cesau78/tektonology/3d-models/prayer-sole/v3-compound-fastened/sole-prayers/jerome-lucido/jerome-lucido-tread-body.stl

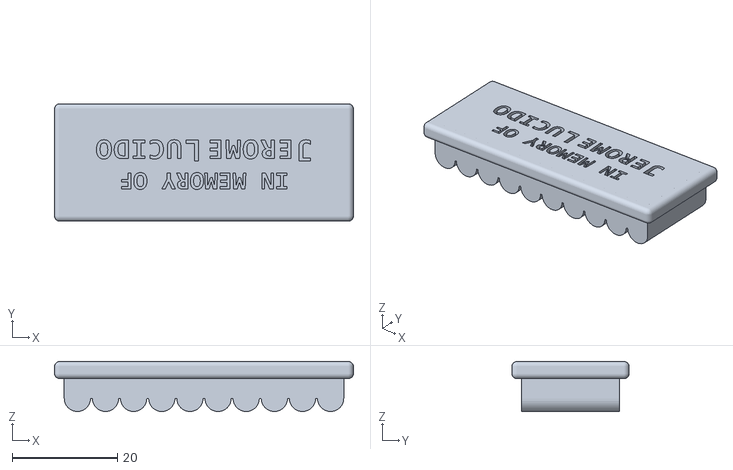
[picture p15: CAD file, 2026-05-01]
3d-models/prayer-sole/v3-compound-fastened/sole-prayers/jerome-lucido/jerome-lucido-tread-body.stl
56.8 x 22.3 x 9.50
