cesau78/tektonology/3d-models/prayer-sole/v3-compound-fastened/sole-prayers/praise-the-lord/praise-the-lord-tread-body.stl

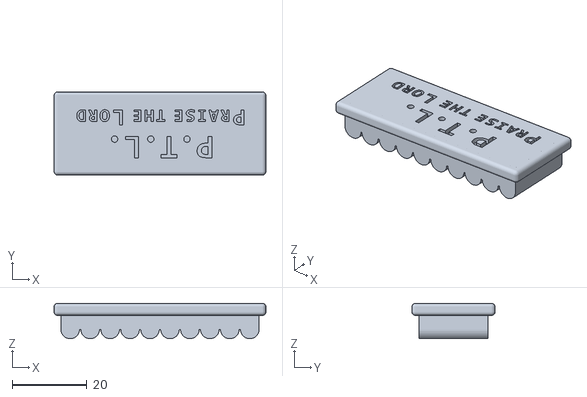
[picture p16: CAD file, 2026-04-18]
3d-models/prayer-sole/v3-compound-fastened/sole-prayers/praise-the-lord/praise-the-lord-tread-body.stl
56.8 x 22.3 x 9.50
