cesau78/tektonology/3d-models/ptfe-port-dryer-box/ptfe-port-dryer-box.stl

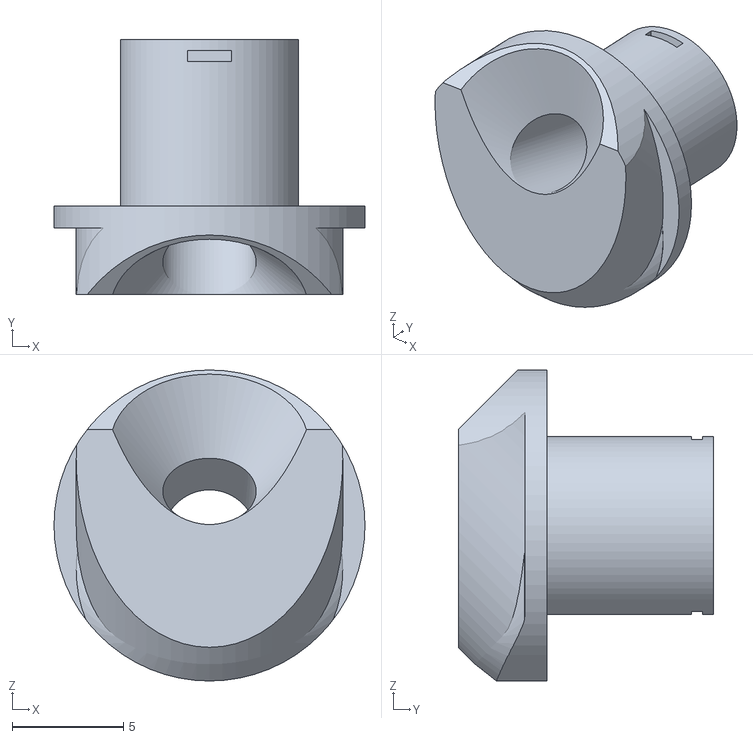
[picture p17: CAD file, 2026-03-22]
3d-models/ptfe-port-dryer-box/ptfe-port-dryer-box.stl
14.0 x 11.5 x 14.0
