cesau78/tektonology/3d-models/ptfe-port-printer-tent/ptfe-port-printer-tent-collar.stl

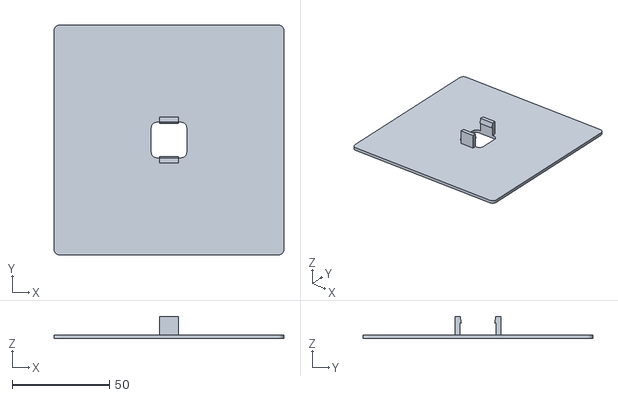
[picture p18: CAD file, 2026-04-04]
3d-models/ptfe-port-printer-tent/ptfe-port-printer-tent-collar.stl
118.0 x 118.0 x 11.5
