cesau78/tektonology/liquid-bait-station/liquid-bait-station.stl

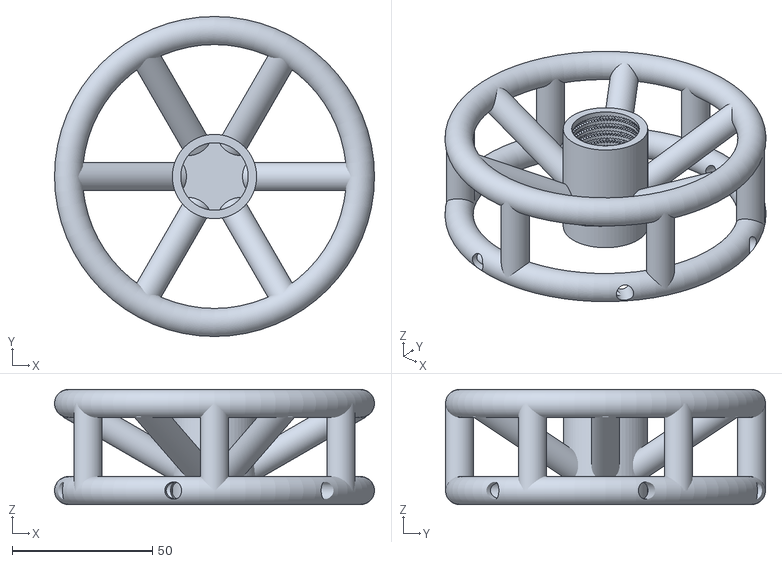
[picture p19: CAD file, 2026-02-21]
liquid-bait-station/liquid-bait-station.stl
113.9 x 113.9 x 41.0
