cesau78/tektonology/tektonology-spa/public/stl/collar.stl

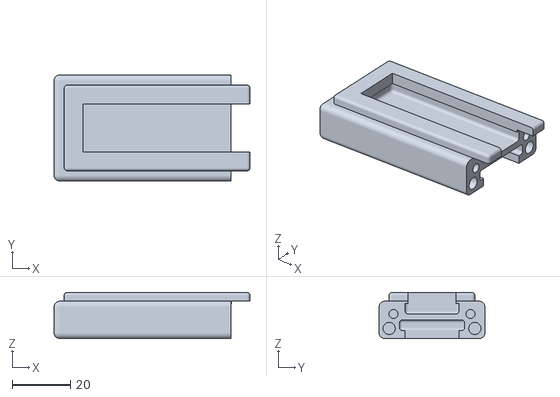
[picture p20: CAD file, 2026-06-22]
tektonology-spa/public/stl/collar.stl
67.5 x 36.5 x 15.8
