cesau78/tektonology/3d-models/notecard-holder/notecard-holder-divider.stl

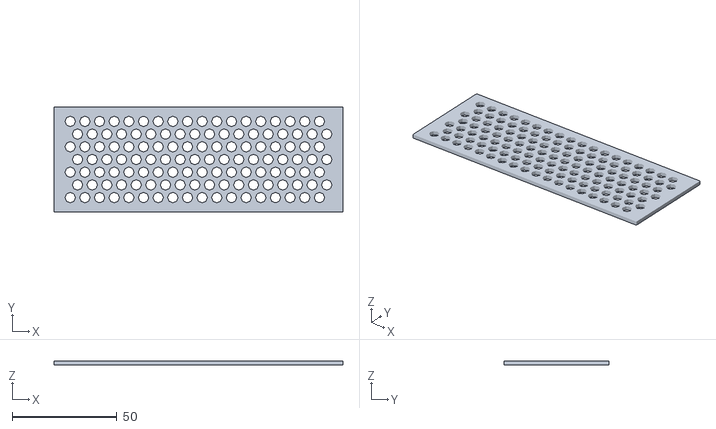
[picture p21: CAD file, 2026-03-11]
3d-models/notecard-holder/notecard-holder-divider.stl
138.0 x 50.3 x 2.00
