cesau78/tektonology/3d-models/prayer-sole/v2-compound-bonded/kneeler-boot-coupler.stl

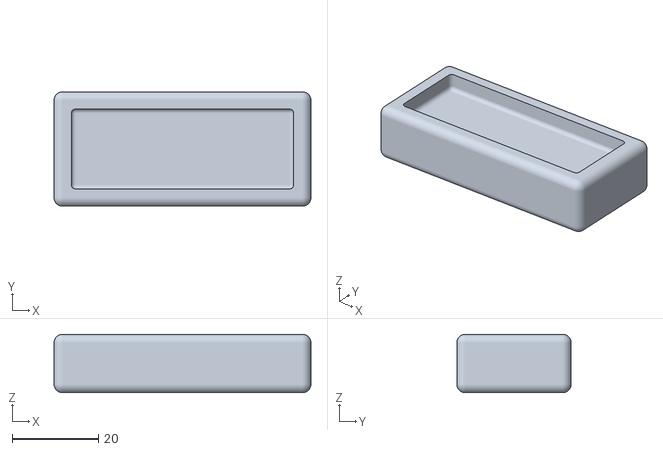
[picture p22: CAD file, 2026-02-20]
3d-models/prayer-sole/v2-compound-bonded/kneeler-boot-coupler.stl
59.5 x 26.5 x 13.5
