cesau78/tektonology/3d-models/prayer-sole/v3-compound-fastened/latest-builds/v3.9.6/collar.stl

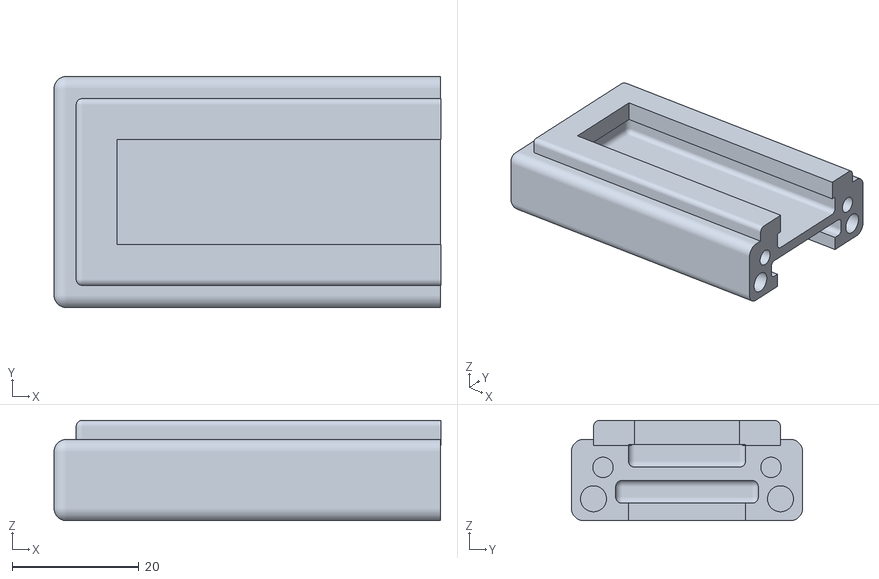
[picture p23: CAD file, 2026-07-21]
3d-models/prayer-sole/v3-compound-fastened/latest-builds/v3.9.6/collar.stl
61.0 x 36.5 x 15.8
