cesau78/tektonology/3d-models/prayer-sole/v3-compound-fastened/sole-prayers/pospie-memorial/pospie-memorial-tread-text.stl

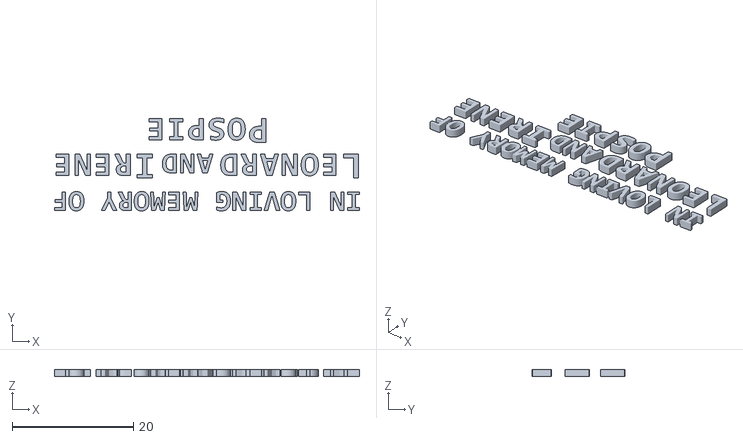
[picture p24: CAD file, 2026-04-18]
3d-models/prayer-sole/v3-compound-fastened/sole-prayers/pospie-memorial/pospie-memorial-tread-text.stl
50.3 x 15.3 x 1.21
