cesau78/tektonology/3d-models/prayer-sole/v3-compound-fastened/sole-prayers/praise-the-lord/praise-the-lord-tread-text.stl

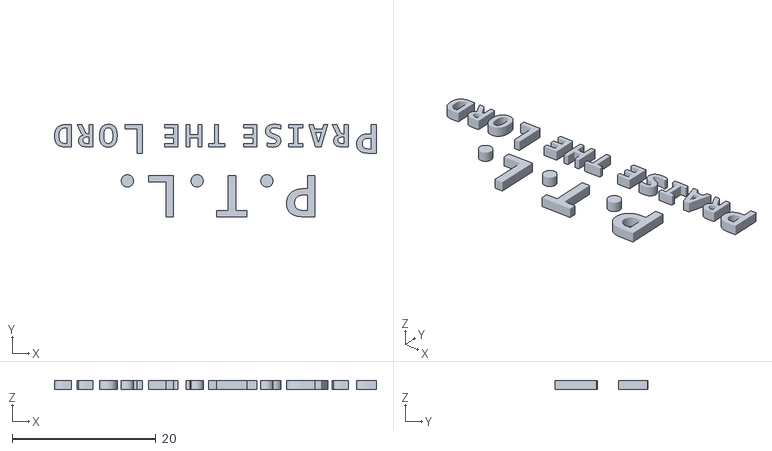
[picture p25: CAD file, 2026-04-18]
3d-models/prayer-sole/v3-compound-fastened/sole-prayers/praise-the-lord/praise-the-lord-tread-text.stl
44.8 x 12.9 x 1.21
