cesau78/tektonology/3d-models/prayer-sole/v3-compound-fastened/sole-prayers/tektonology/tektonology-tread-text.stl

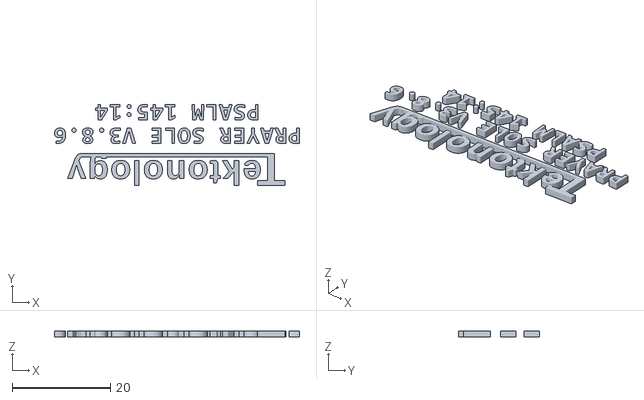
[picture p26: CAD file, 2026-04-18]
3d-models/prayer-sole/v3-compound-fastened/sole-prayers/tektonology/tektonology-tread-text.stl
49.8 x 16.5 x 1.21
