cesau78/tektonology/3d-models/ptfe-port-printer-tent/ptfe-port-printer-tent-shaft.stl

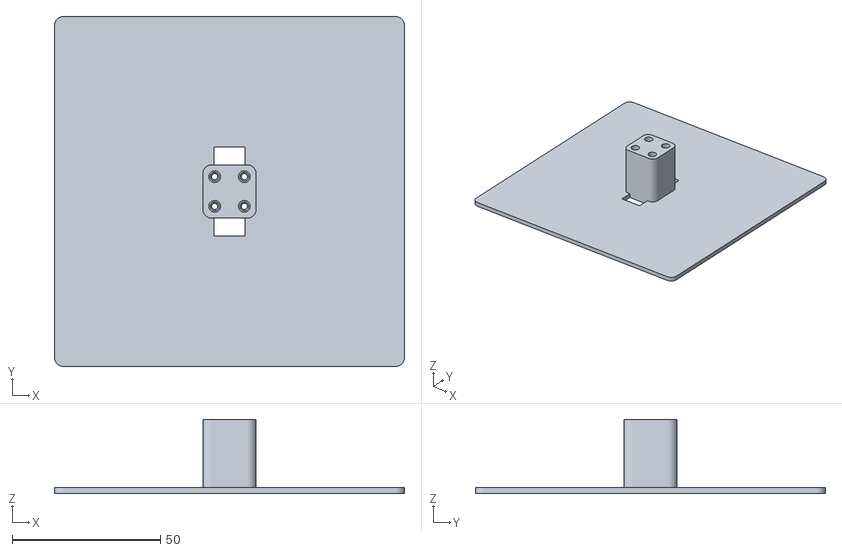
[picture p27: CAD file, 2026-04-04]
3d-models/ptfe-port-printer-tent/ptfe-port-printer-tent-shaft.stl
118.0 x 118.0 x 25.0
