cesau78/tektonology/tektonology-spa/public/stl/cap.stl

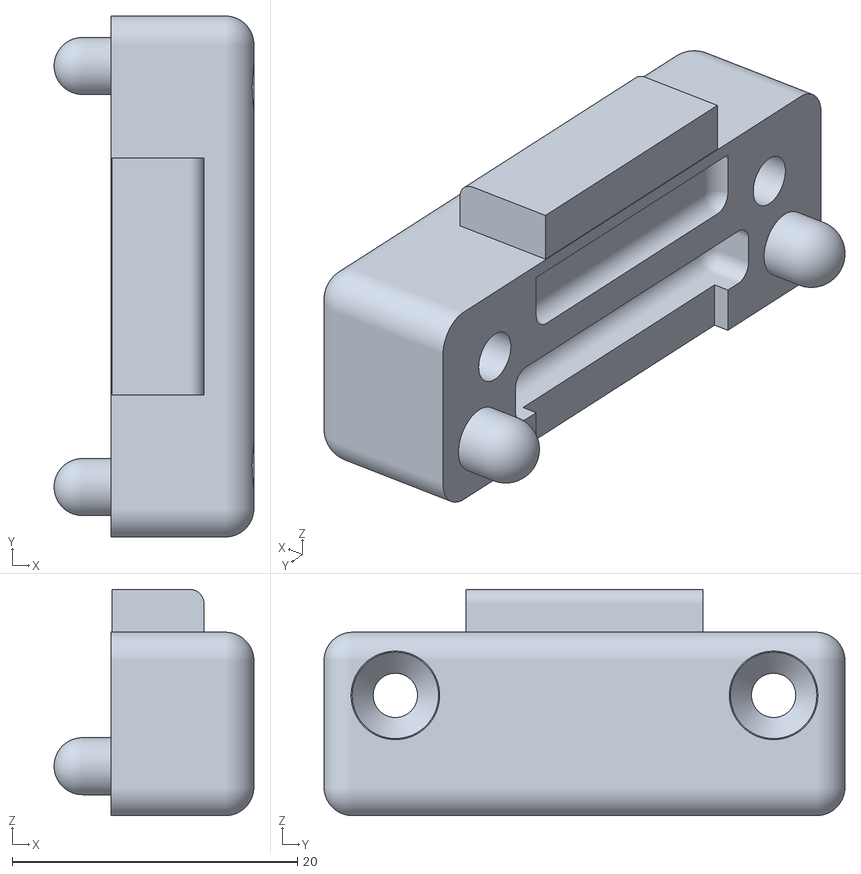
[picture p28: CAD file, 2026-06-22]
tektonology-spa/public/stl/cap.stl
14.0 x 36.5 x 15.8
