cesau78/tektonology/3d-models/notecard-holder/notecard-holder-side.stl

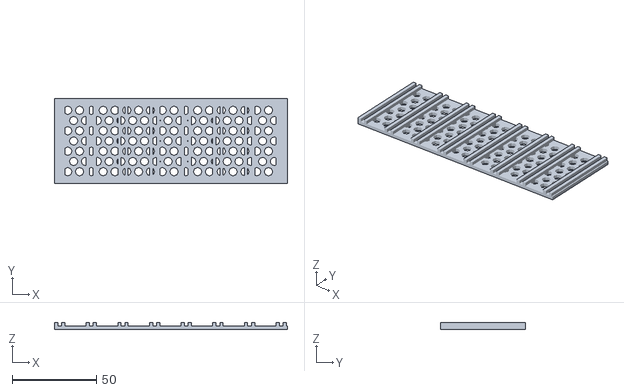
[picture p29: CAD file, 2026-03-11]
3d-models/notecard-holder/notecard-holder-side.stl
138.1 x 50.3 x 4.00
