cesau78/tektonology/tektonology-spa/public/stl/kneeler-bracket-left.stl

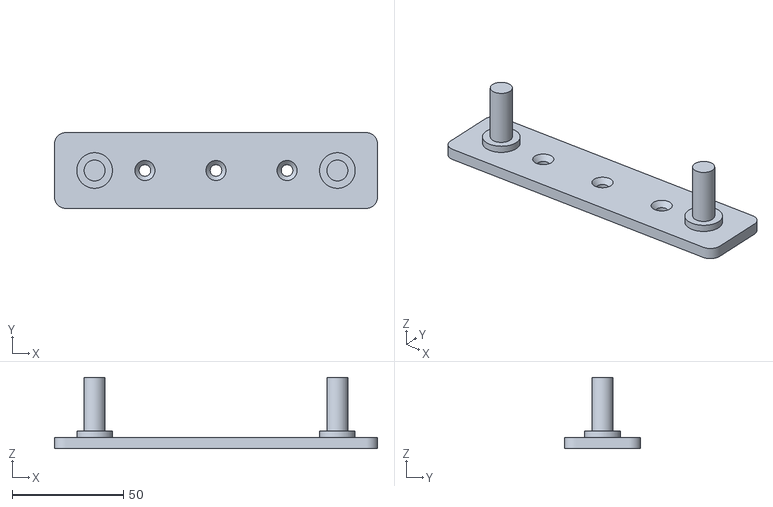
[picture p30: CAD file, 2026-05-03]
tektonology-spa/public/stl/kneeler-bracket-left.stl
145.0 x 34.0 x 32.0
