cesau78/tektonology/tektonology-spa/public/stl/kneeler-boot-slipper.stl

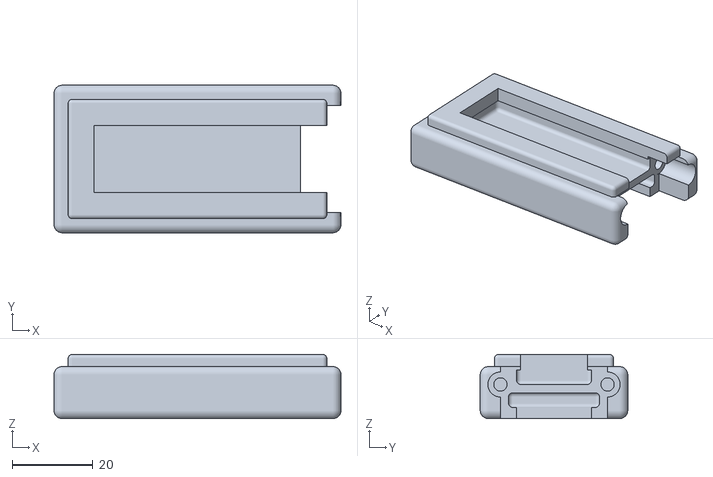
[picture p31: CAD file, 2026-03-23]
tektonology-spa/public/stl/kneeler-boot-slipper.stl
71.0 x 36.5 x 15.8
