cesau78/tektonology/tektonology-spa/public/stl/allen-wrench-handle.stl

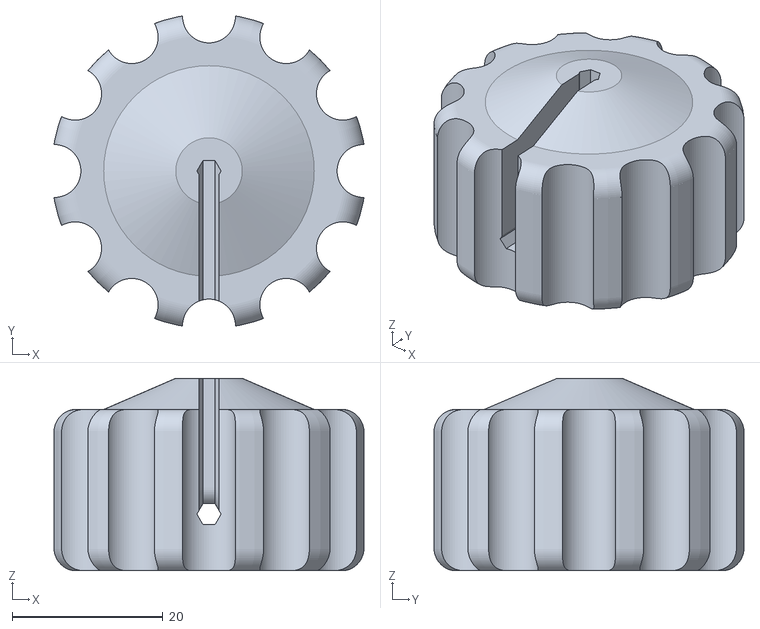
[picture p32: CAD file, 2026-03-20]
tektonology-spa/public/stl/allen-wrench-handle.stl
41.1 x 41.1 x 25.5
