cesau78/tektonology/tektonology-spa/public/stl/kneeler-boot-cap.stl

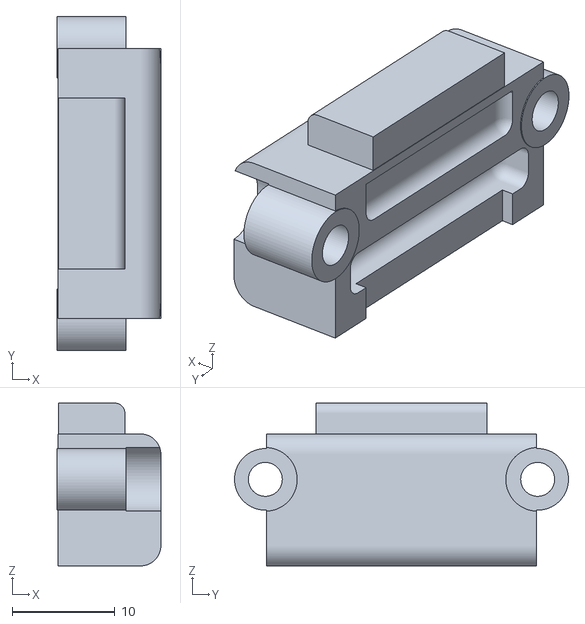
[picture p33: CAD file, 2026-03-14]
tektonology-spa/public/stl/kneeler-boot-cap.stl
10.1 x 32.5 x 15.8
