cesau78/tektonology/3d-models/kneeler-replacement-parts/kneeler-boot-compound-fastened/kneeler-boot-config.scad

// --- TEKTONOLOGY KNEELER BOOT CONFIG ---
// Shared parameters and modules for the 2-piece coupler (slipper + cap)

tolerance = 0.1; // general tolerance for fit adjustments (mm)

// --- Sole Plate Dimensions ---
sole_plate_l = 53;
sole_plate_w = 18.5;
sole_plate_h = 3.5;

// --- Leg Dimensions (for socket fit) ---
leg_w = 16.5;
leg_l = 51;

// --- Bottom Slide Groove (shared between coupler + insert) ---
groove_overhang = 2;      // groove extends this far beyond socket per side

// --- Performance Settings ---
preview = false; //set preview=true for faster rendering with lower detail, or false for full detail.
crosssection_view = false; // Set to true to cut the model along a plane and show only one side
crosssection_axis = "y"; // axis: 'x', 'y', or 'z'
crosssection_pos = 12; // position (mm) along the chosen axis where the cut occurs (default 0 = origin)

// --- Shell Geometry ---
wall = 9.0; // thicker walls to house M3 hardware in the side walls
floor_thickness = 3.0; // thickness of the shell floor under the bottom socket

bottom_target_depth = 6.35;
total_h = sole_plate_h + bottom_target_depth + floor_thickness;
r = 2.0;
$fn = preview ? 32 : 64;

// --- Lip Parameters ---
enable_top_lip = true;
lip_inset = 1;
lip_thickness = 3;
lip_height = 1;  // Z thickness of cap lip relief cut in slipper

// --- Two-Piece Split ---
cap_thickness = 8; // along X axis
split_x = (sole_plate_l / 2) + wall - r - cap_thickness;

// --- Derived ---
outer_extent = (sole_plate_l / 2) + wall; // half-length of outer shell after minkowski
cap_width = sole_plate_w + (groove_overhang * 2) + 4; // cap Y width matches bottom groove (including minkowski)
// Lip ring inner opening dimensions (used for lip splitting)
lip_inner_x = leg_l + tolerance;
lip_inner_y = leg_w + tolerance; // add some clearance around the leg for easy fit and print tolerance

// --- M3x30 Socket Head Cap Screw Hardware ---
bolt_dia        = 3.0;
bolt_clearance  = 0.3;  // clearance for bolt holes (0 for snug fit, increase if needed for print tolerance)
bolt_length     = 20;   // M3x20 — shaft length under head (very common size)
nut_af          = 5.5;  // hex nut across-flats
nut_clearance   = 0.2;  // clearance for nut pockets
nut_thickness   = 2.4;  // typical M3 nut thickness, adjust if using thinner/heavier nuts
head_dia        = 6.0;  // M3 socket head cap screw head diameter
head_clearance  = tolerance;
head_height     = 3.5;   // M3 socket head height

// Nut X position: derived so bolt tip fully engages the nut with 0.5mm margin
// bolt shaft starts at outer_extent - head_height, tip = start - bolt_length
nut_x = (outer_extent - head_height) - bolt_length + (nut_thickness / 2) + 0.5;

// Bolt position: two screws aligned with cap side bosses (Y = ±cap_width/2)
bolt_z = (bolt_dia / 2) + 0.5; // bottom of bolt hole 0.5mm above z=0
bolt_positions = [[bolt_z, cap_width / 2], [bolt_z, -cap_width / 2]];

// --- Cap Side Bosses ---
boss_dia       = head_dia;    // matches cap screw head diameter
boss_height    = head_height; // adjust with screw availability
boss_clearance = tolerance; // clearance per side between cap boss and slipper socket

// --- Alignment Tongue ---
tongue_width     = 10;   // along Y
tongue_height    = 6;    // along Z
tongue_depth     = 1.5;  // protrusion along X
tongue_clearance = tolerance;

// --- Big constant for half-space clipping ---
big = 200;

// =====================================================================
// COUPLER SHELL — outer shell + sockets, WITHOUT the top lip
// =====================================================================
module coupler_shell() {
    module inner_cuts() {
        // TOP SOCKET (Metal Leg) — beveled/rounded walls
        translate([0, 0, (total_h / 2) - (sole_plate_h / 2) + tolerance])
            minkowski() {
                cube([leg_l, leg_w, sole_plate_h], center=true);
                sphere(r=1.0);
            }

        // BOTTOM SOCKET (TPU Plug) — flat walls
        translate([0, 0, -(total_h / 2) + (bottom_target_depth / 2) - tolerance])
            cube([sole_plate_l, sole_plate_w, bottom_target_depth + 0.2], center=true);

        // BOTTOM SOCKET SLIDE GROOVE — rounded perimeter, wider than socket for slide-in rail
        // 1/4 socket depth, top aligned to top of bottom socket
        groove_h = bottom_target_depth / 4;
        translate([0, 0, -(total_h / 2) + bottom_target_depth - (groove_h / 2) - 1])
            minkowski() {
                cube([
                    sole_plate_l + (groove_overhang * 2) - 2,
                    sole_plate_w + (groove_overhang * 2) - 2,
                    groove_h
                ], center=true);
                sphere(r=1.0);
            }
    }

    difference() {
        minkowski() {
            cube([
                sole_plate_l + (wall * 2) - (r * 2),
                sole_plate_w + (wall * 2) - (r * 2),
                total_h - (r * 2)
            ], center=true);
            sphere(r=r);
        }
        inner_cuts();
    }
}

// =====================================================================
// TOP SOCKET CUT — reusable for re-cutting after lip is added
// =====================================================================
module top_socket_cut() {
    // Flat cut — shaves 2*tolerance off the underside of the lip
    cut_h = tolerance * 2;
    lip_r = 1.0;
    lip_bottom_z = (total_h / 2) - lip_r + (lip_thickness / 2) - (lip_thickness / 2);
    translate([0, 0, lip_bottom_z + (cut_h / 2)])
        cube([sole_plate_l, sole_plate_w, cut_h], center=true);
}

// =====================================================================
// TOP LIP — standalone module (full rectangular ring)
// =====================================================================
module top_lip() {
    lip_r = 1.0; // Minkowski rounding radius for lip
    // Positioned so flat bottom overlaps shell top by lip_r for bonded fit
    lip_z = (total_h / 2) - lip_r + (lip_thickness / 2);
    cut_z = lip_z - (lip_thickness / 2); // flat bottom plane
    outer_x = sole_plate_l + wall;
    outer_y = sole_plate_w + wall;

    intersection() {
        translate([0, 0, lip_z])
        difference() {
            minkowski() {
                cube([outer_x, outer_y, lip_thickness], center=true);
                sphere(r=lip_r);
            }
            // Ring cutout
            cube([lip_inner_x, lip_inner_y, lip_thickness + 2], center=true);
            // Underside relief
            translate([0, 0, -(lip_thickness / 2) - 1])
                minkowski() {
                    cube([leg_l, leg_w, 0.01], center=true);
                    sphere(r=lip_r);
                }
        }
        // Remove bottom Minkowski rounding for flat bonded fit to slipper
        translate([-big, -big, cut_z])
            cube([big * 2, big * 2, big * 2]);
    }
}

// =====================================================================
// SPLIT LIP MODULES
// =====================================================================

// Slipper lip: full ring MINUS the far short-end bar (cap's portion).
module slipper_lip() {
    intersection() {
        top_lip();
        union() {
            translate([-big, -big, -big])
                cube([big + lip_inner_x / 2, big * 2, big * 2]);
            translate([-big, lip_inner_y / 2, -big])
                cube([big * 2, big, big * 2]);
            translate([-big, -big - lip_inner_y / 2, -big])
                cube([big * 2, big, big * 2]);
        }
    }
}

// Cap lip: only the far short-end bar between the slipper's overhanging lips.
module cap_lip() {
    intersection() {
        top_lip();
        translate([lip_inner_x / 2, -lip_inner_y / 2, -big])
            cube([big, lip_inner_y, big * 2]);
    }
}

// =====================================================================
// HALF-SPACE helpers
// =====================================================================

module slipper_half_space() {
    translate([-big, -big, -big])
        cube([big + split_x, big * 2, big * 2]);
}

module cap_half_space() {
    translate([split_x, -big, -big])
        cube([big, big * 2, big * 2]);
}

// Side-wall Y bands (material outside the cap width)
module side_bands() {
    // +Y band
    translate([-big, cap_width / 2, -big])
        cube([big * 2, big, big * 2]);
    // -Y band
    translate([-big, -big - cap_width / 2, -big])
        cube([big * 2, big, big * 2]);
}

// Center Y band (material inside the socket footprint)
module center_band() {
    translate([-big, -sole_plate_w / 2, -big])
        cube([big * 2, sole_plate_w, big * 2]);
}

// =====================================================================
// CROSS-SECTION SUPPORT
// =====================================================================
module crosssection(half_space) {
    if (!crosssection_view) {
        children();
    } else {
        intersection() {
            children();
            if (crosssection_axis == "x")
                translate([crosssection_pos, -half_space, -half_space])
                    cube([half_space * 2, half_space * 2, half_space * 2]);
            if (crosssection_axis == "y")
                translate([-half_space, crosssection_pos, -half_space])
                    cube([half_space * 2, half_space * 2, half_space * 2]);
            if (crosssection_axis == "z")
                translate([-half_space, -half_space, crosssection_pos])
                    cube([half_space * 2, half_space * 2, half_space * 2]);
        }
    }
}

// =====================================================================
// DEBUG: visualize hex nuts in their pockets
// =====================================================================
module debug_nuts() {
    nut_r = nut_af / 2 / cos(30);
    color("green", 0.7)
        for (pos = bolt_positions) {
            rot = (pos[1] > 0) ? 15 : -15; // mirror matches slipper's mirror([0,m,0])
            translate([nut_x, pos[1], pos[0]])
                rotate([0, 90, 0])
                    rotate([0, 0, rot])
                        cylinder(h=nut_thickness, r=nut_r, $fn=6, center=true);
        }
}

// =====================================================================
// DEBUG: visualize bolts in their holes
// =====================================================================
module debug_bolts() {
    head_start_x = outer_extent - head_height;
    color("yellow", 0.7)
        for (pos = bolt_positions) {
            // Shaft
            translate([head_start_x - bolt_length, pos[1], pos[0]])
                rotate([0, 90, 0])
                    cylinder(h=bolt_length, d=bolt_dia, center=false);
            // Socket head
            translate([head_start_x, pos[1], pos[0]])
                rotate([0, 90, 0])
                    cylinder(h=head_height, d=head_dia, center=false);
        }
}
