cesau78/tektonology/3d-models/bumper-bracket/bumper-bracket.scad

// Bumper bracket body: shell envelope (core + roof wedge + pew pad) pre-mink, then fillet + cutters.
// Drawn in bracket coordinates (see config.scad). No rotate() reorients the bracket body.

include <config.scad>

// Includers (cap.scad, tread-carriage.scad, …) set BUMPER_BRACKET_INCLUDED_BY = true
// before `include <bumper-bracket.scad>` so only the host file emits root geometry.
$fn = preview ? 32 : 64;

// Core, roof overlap + prism, and pew pad — shared envelope anchors, no per-part minkowski.
module shell_envelope_pre_mink(overlap_below = corner_r) {
    core_c = shell_envelope_core_center_lxlz();
    wedge_xr = shell_envelope_wedge_xr_lx_mm();
    wedge_run = shell_inset_dim_qr_wedge_mm;
    wedge_depth = shell_inset_dim_tread_pew_mm;

    intersection() {
        union() {
            translate(bracket_pos(core_c[0], core_c[1], core_c[2]))
                cube(
                    [shell_envelope_core_lx_mm, shell_envelope_core_lz_mm, shell_envelope_core_ly_mm],
                    center = true
                );

            translate(bracket_pos(
                shell_envelope_inset_lx_mm + wedge_run / 2,
                shell_envelope_inset_ly_mm + wedge_depth / 2,
                shell_envelope_roof_lz_mm - overlap_below / 2
            ))
                cube([wedge_run, overlap_below, wedge_depth], center = true);

            polyhedron(
                points = [
                    bracket_pos(shell_envelope_inset_lx_mm, shell_envelope_inset_ly_mm, shell_envelope_roof_lz_mm),
                    bracket_pos(wedge_xr, shell_envelope_inset_ly_mm, shell_envelope_roof_lz_mm),
                    bracket_pos(wedge_xr, shell_envelope_inset_ly_mm, shell_envelope_apex_lz_mm),
                    bracket_pos(shell_envelope_inset_lx_mm, shell_envelope_inset_ly_mm + wedge_depth, shell_envelope_roof_lz_mm),
                    bracket_pos(wedge_xr, shell_envelope_inset_ly_mm + wedge_depth, shell_envelope_roof_lz_mm),
                    bracket_pos(wedge_xr, shell_envelope_inset_ly_mm + wedge_depth, shell_envelope_apex_lz_mm),
                ],
                faces = [
                    [0, 1, 4, 3],
                    [1, 2, 5, 4],
                    [0, 3, 5, 2],
                    [0, 2, 1],
                    [3, 4, 5],
                ],
                convexity = 4
            );

            // Front (+Y) end extended by pew_mount_block_face_extend_y_mm and tilted by
            // pew_mount_block_face_angle_deg, built straight into the pre-mink primitive as
            // an extruded X-Y footprint (front edge follows the tilt line). This way the
            // angle gets the same minkowski rounding and renders cleanly — no post-mink cut.
            if (pew_mount_block_enabled && pew_mount_block_y_len_mm > 0.2) {
                blk_x_lo = pew_mount_block_x_center_mm() - pew_mount_block_thickness_x_mm / 2;
                blk_x_hi = pew_mount_block_x_center_mm() + pew_mount_block_thickness_x_mm / 2;
                blk_y_lo = pew_mount_block_y_lo_mm();
                translate([0, 0, pew_mount_block_z_center_mm() - pew_mount_block_z_len_mm() / 2])
                    linear_extrude(pew_mount_block_z_len_mm())
                        polygon([
                            [blk_x_lo, blk_y_lo],
                            [blk_x_hi, blk_y_lo],
                            [blk_x_hi, pew_mount_block_front_y_at(blk_x_hi)],
                            [blk_x_lo, pew_mount_block_front_y_at(blk_x_lo)],
                        ]);
            }

            // Reinforcement welded to the block's −X side: full block Z height, from the
            // roof-wedge start out to the block's tilted +Y front. A pre-mink primitive so
            // it rounds and welds flush; its front edge shares the same tilt line as the block.
            if (pew_mount_reinforce_enabled && pew_mount_block_enabled && pew_mount_block_y_len_mm > 0.2) {
                rx_hi = pew_mount_block_x_center_mm() - pew_mount_block_thickness_x_mm / 2;
                rx_lo = rx_hi - pew_mount_reinforce_depth_x_mm;
                ry_lo = bracket_nat_y_mid_mm - shell_height_mm;   // roof-wedge start (core/wedge seam)
                translate([0, 0, pew_mount_block_z_center_mm() - pew_mount_block_z_len_mm() / 2])
                    linear_extrude(pew_mount_block_z_len_mm())
                        polygon([
                            [rx_lo, ry_lo],
                            [rx_hi, ry_lo],
                            [rx_hi, pew_mount_block_front_y_at(rx_hi)],
                            [rx_lo, pew_mount_block_front_y_at(rx_lo)],
                        ]);
            }

        }

        // Rectangular hull clip: remove all geometry below y = -25 before minkowski.
        // Hull of two large flat slabs produces a clean rectangular prism y ≥ -25.
        _pre_mink_y_floor_hull();
    }
}

module _pre_mink_y_floor_hull() {
    big = _bracket_cross_half_extent();
    hull() {
        translate([-big, -25, -big]) cube([2 * big, 1, 2 * big]);
        translate([-big,  big, -big]) cube([2 * big, 1, 2 * big]);
    }
}

// Two hull cutters, one per gap between the 3 roof screws (fracs 1/6, 1/2, 5/6).
// Centered at inter-screw midpoints (fracs 1/3 and 2/3), Z height = half the
// inter-screw spacing. Subtracted pre-minkowski so cut edges get the sphere fillet.
module _pre_mink_screw_gap_tabs_cut() {
    tab_z_half = shell_inset_dim_tread_pew_mm / 12;
    for (pair = [
        [-screw_gap_tab_z_nudge_mm, 1/3],   // bottom tab, shifted −Z
        [ screw_gap_tab_z_nudge_mm, 2/3],   // top tab, shifted +Z
    ])
        _pre_mink_screw_gap_tab(
            corner_r + shell_inset_dim_tread_pew_mm * pair[1] - shell_extent_tread_pew_mm / 2 + pair[0],
            tab_z_half
        );
}

// Rectangular hull cutter: X −20→+30, Y −25→0, Z centered at z_center ± z_half.
module _pre_mink_screw_gap_tab(z_center, z_half) {
    c = HULL_VERTEX_CUBE_MM;
    hull()
        for (x = [-20, 30], y = [-25, 0], z = [z_center - z_half, z_center + z_half])
            translate([x, y, z])
                cube(c, center = true);
}

function bracket_world_z_min() = bracket_face_tread_slot_z_mm;

// Exported carriage min Z after post-extraction −Z shave (bed lift only).
function tread_carriage_world_z_min() =
    tread_carriage_sel_z_lo_bracket() + tread_carriage_z_lo_trim_mm;

// Absolute bracket-frame selection prism for tread-carriage extraction.
module tread_carriage_selection_cube() {
    translate([
        tread_carriage_x_lo_mm,
        tread_carriage_y_lo_mm,
        tread_carriage_sel_z_lo_bracket(),
    ])
        cube([
            tread_carriage_x_hi_mm - tread_carriage_x_lo_mm,
            tread_carriage_y_hi_mm - tread_carriage_y_lo_mm,
            tread_carriage_sel_z_hi_bracket() - tread_carriage_sel_z_lo_bracket(),
        ]);
}

// Shave slabs off the extracted carriage solid; selection cube / bracket cavity unchanged.
module tread_carriage_post_extract_trim() {
    trim_margin = 10;
    difference() {
        children();
        if (tread_carriage_x_lo_trim_mm > 0)
            translate([
                tread_carriage_x_lo_mm,
                tread_carriage_y_lo_mm - trim_margin,
                tread_carriage_sel_z_lo_bracket() - trim_margin,
            ])
                cube([
                    tread_carriage_x_lo_trim_mm,
                    tread_carriage_y_hi_mm - tread_carriage_y_lo_mm + 2 * trim_margin,
                    tread_carriage_sel_z_hi_bracket() - tread_carriage_sel_z_lo_bracket()
                        + 2 * trim_margin,
                ]);
        if (tread_carriage_z_lo_trim_mm > 0)
            translate([
                tread_carriage_x_lo_mm - trim_margin,
                tread_carriage_y_lo_mm - trim_margin,
                tread_carriage_sel_z_lo_bracket(),
            ])
                cube([
                    tread_carriage_x_hi_mm - tread_carriage_x_lo_mm + 2 * trim_margin,
                    tread_carriage_y_hi_mm - tread_carriage_y_lo_mm + 2 * trim_margin,
                    tread_carriage_z_lo_trim_mm,
                ]);
    }
}

// Fused cap: union the plug into the body first, then cut screw-head recesses and
// chamfers through the combined solid. Cutting them inside earlier booleans clips
// material at exterior faces (minkowski skin, cap ∩ shell, etc.).
module shell_body_with_integrated_cap() {
    difference() {
        union() {
            children();
            tread_cap_solid(0, cut_bolt_hole = false);
        }
        shell_body_late_screw_cuts();
    }
}

// Head recesses and chamfers — subtract after the shell body (and fused cap) are united.
module shell_body_late_screw_cuts() {
    if (wood_screw_holes_enabled)
        wood_screw_chamfer_pattern();
    if (side_screw_enabled && pew_mount_block_enabled && pew_mount_block_y_len_mm > 0.2)
        side_screw_chamfer();
    if (tread_cap_enabled && !tread_cap_separate_print)
        tread_cap_bolt_hole();
}

// Full shell body minus the tread-carriage region (when split is enabled).
// Integrated cap (tread_cap_separate_print = false) always stays on the bracket.
module bumper_bracket_shell_body() {
    if (tread_carriage_split_enabled) {
        if (tread_cap_enabled && !tread_cap_separate_print)
            shell_body_with_integrated_cap()
                difference() {
                    shell_body_main_difference();
                    tread_carriage_selection_cube();
                }
        else
            difference() {
                difference() {
                    shell_body_main_difference();
                    tread_carriage_selection_cube();
                }
                shell_body_late_screw_cuts();
            }
    } else {
        shell_body_difference_wedge_bores();
    }
}

// Geometry inside tread_carriage_selection_cube() for a separate print.
module tread_carriage() {
    tread_carriage_post_extract_trim()
        intersection() {
            shell_body_main_difference();
            tread_carriage_selection_cube();
        };
}

// Export-only Z translate (not a design-frame rotation).
module tread_carriage_export_bed_lift() {
    if (bracket_lift_to_bed)
        translate([0, 0, -tread_carriage_world_z_min()])
            children();
    else
        children();
}

// Export-only Z translate (not a design-frame rotation).
module bracket_export_bed_lift() {
    if (bracket_lift_to_bed)
        translate([0, 0, -bracket_world_z_min()])
            children();
    else
        children();
}

function exploded_tread_offset_vec() = [
    exploded_tread_offset_pull[0],
    exploded_tread_offset_pull[1] + assembly_tread_vertical_auto_mm() + assembly_tread_z_trim_mm,
    exploded_tread_offset_pull[2],
];

function _bracket_cross_half_extent() =
    max(
        shell_extent_qr_wedge_mm,
        shell_extent_tread_pew_mm,
        shell_height_mm + shell_wedge_leg_mm
    ) * 2 + 40;

module _bracket_cross_half_space_positive() {
    h = _bracket_cross_half_extent();
    pos =
        (bracket_cross_axis == "x" ? 0
        : bracket_cross_axis == "y" ? shell_midplane_y_mm
        : 0) + bracket_cross_offset;
    if (bracket_cross_axis == "x")
        translate([pos, -h, -h])
            cube([2 * h, 2 * h, 2 * h]);
    else if (bracket_cross_axis == "y")
        translate([-h, pos, -h])
            cube([2 * h, 2 * h, 2 * h]);
    else
        translate([-h, -h, pos])
            cube([2 * h, 2 * h, 2 * h]);
}

module bracket_cross_trim() {
    if (!bracket_cross_section) {
        children();
    } else {
        intersection() {
            union() {
                children();
            }
            _bracket_cross_half_space_positive();
        }
    }
}

// One minkowski fillet over the pre-mink envelope union (tread ghost uses its own
// minkowski separately). Pre-mink cuts (undercut, screw-gap tabs) are subtracted
// BEFORE the sphere sweep so their edges receive the same fillet as the solid faces.
module shell_envelope_minkowski_union(undercut = false) {
    minkowski() {
        difference() {
            shell_envelope_pre_mink();
            if (undercut && pew_mount_block_undercut_enabled && pew_mount_block_enabled && pew_mount_block_y_len_mm > 0.2)
                pew_mount_block_bottom_undercut_cut();
            _pre_mink_screw_gap_tabs_cut();
        }
        sphere(r = corner_r, $fn = preview ? 16 : 24);
    }
}

// Solid rule cube minus three rectangular hull(CUBE) cutters on the 9.8° E-bevel plane (no polyhedron).
// (HULL_VERTEX_CUBE_MM lives in config.scad — the QR face-angle derivation needs it.)

function y_on_e_bevel_plane(z) =
    bracket_nat_y_mid_mm - tread_face_e_bevel_slope_k() * (bracket_face_pew_z_mm - z);

// Frustum with sloped top/bottom at y_top(z) and y_bot(z); sides vertical in Y (parallel to bevel normal stack).
module hull_rect_on_e_slope(x_lo, x_hi, z_lo, z_hi, y_top_lo, y_top_hi, y_bot_lo, y_bot_hi) {
    c = HULL_VERTEX_CUBE_MM;
    hull() {
        for (p = [
            [x_lo, y_bot_lo, z_lo],
            [x_hi, y_bot_lo, z_lo],
            [x_lo, y_bot_hi, z_hi],
            [x_hi, y_bot_hi, z_hi],
            [x_lo, y_top_lo, z_lo],
            [x_hi, y_top_lo, z_lo],
            [x_lo, y_top_hi, z_hi],
            [x_hi, y_top_hi, z_hi],
        ])
            translate(p)
                cube(c, center = true);
    }
}

// Cutter 1: E-bevel wedge above y_on_e_bevel_plane (0 at C∩E, tread_face_d_e_side_y_narrow_mm at D∩E).
module shell_tread_face_de_bevel_cut() {
    z_d = bracket_face_tread_slot_z_mm;
    z_c = bracket_face_pew_z_mm;
    y_e = bracket_nat_y_mid_mm;
    y_hi = y_e + shell_wedge_leg_mm + 40;
    x_h = shell_extent_qr_wedge_mm / 2 + shell_wedge_leg_mm + 20;

    // When the pew mount block extends in +Y past the E-bevel plane, stop the
    // bevel cutter at the block's −X face so the angled top sits flush against
    // the block's side wall instead of slicing diagonally through the cube. If
    // the −X reinforcement is present, stop at its −X face so it stays flush too.
    // The hull vertex cubes are CENTERED on the bound, so pull it in by half a
    // cube so the cut plane lands exactly ON the flush face instead of 0.25 mm
    // into it (that bite also ate into the QR front face's −X border).
    block_minus_x = pew_mount_block_x_center_mm() - pew_mount_block_thickness_x_mm / 2;
    flush_x = (pew_mount_reinforce_enabled && pew_mount_block_enabled && pew_mount_block_y_len_mm > 0.2)
        ? block_minus_x - pew_mount_reinforce_depth_x_mm
        : block_minus_x;
    x_hi = (pew_mount_block_enabled && pew_mount_block_y_len_mm > 0.2)
        ? flush_x - HULL_VERTEX_CUBE_MM / 2
        : x_h;

    hull_rect_on_e_slope(
        -x_h,
        x_hi,
        z_d,
        z_c,
        y_hi,
        y_hi,
        y_on_e_bevel_plane(z_d),
        y_on_e_bevel_plane(z_c)
    );
}

function hyp_z_at_x(x) =
    shell_wedge_leg_mm * (x - corner_r) / shell_wedge_hypotenuse_run_mm;

module wood_mount_hole_shank(y_frac) {
    psi_deg = atan2(shell_wedge_leg_mm, shell_wedge_hypotenuse_run_mm);
    $fn = preview ? 28 : 64;

    // rotate([-90,0,0]): local +Z = hypotenuse outward normal (leg, run) in bracket X–Y.
    translate(wood_screw_hole_exterior_bracket_pos(y_frac))
        rotate([0, 0, -psi_deg])
            rotate([-90, 0, 0])
                cylinder(h = wood_bored_axial_mm, d = wood_shank_clr, center = true);
}

module wood_mount_hole_chamfer(y_frac) {
    psi_deg = atan2(shell_wedge_leg_mm, shell_wedge_hypotenuse_run_mm);
    head_d = wood_head_diameter + 2 * screw_chamfer_lip_mm;
    shank_d = wood_shank_clr + epsilon * 2;
    head_r = head_d / 2;
    shank_r = shank_d / 2;
    half_ang = wood_screw_chamfer_half_angle_deg();
    flare_depth = (head_r - shank_r) / tan(half_ang);
    over = corner_r + epsilon * 4;
    $fn = preview ? 32 : 64;

    // #8 wood screw head flare: wide at exterior skin (d2), tapers −Z to shank (d1).
    // Subtracted in shell_body_late_screw_cuts() after all unions so the cone is not
    // clipped by the minkowski skin or earlier booleans.
    translate(wood_screw_hole_exterior_bracket_pos(y_frac))
        rotate([0, 0, -psi_deg])
            rotate([0, 90, 270])
                translate([0, 0, -flare_depth - over + 0.3])
                    cylinder(h = flare_depth + over, d1 = shank_d, d2 = head_d);
}

module wood_screw_shank_pattern() {
    for (yf = wood_screw_hole_y_fractions)
        wood_mount_hole_shank(yf);
}

module wood_screw_chamfer_pattern() {
    for (yf = wood_screw_hole_y_fractions)
        wood_mount_hole_chamfer(yf);
}

// Cutter 2/3: rectangular pocket; ceiling on y_on_e_bevel_plane − ceiling_drop; floor parallel below by depth_y.
module shell_tread_pocket_sloped_hull(lx_center, ly_center, pocket_w, pocket_len_ly, depth_y, ceiling_drop_mm) {
    z_d = bracket_face_tread_slot_z_mm;
    ly_lo = ly_center - pocket_len_ly / 2;
    ly_hi = ly_center + pocket_len_ly / 2;
    z_lo = min(ly_lo - shell_extent_tread_pew_mm / 2, z_d - epsilon * 4);
    z_hi = ly_hi - shell_extent_tread_pew_mm / 2;
    z_pad = epsilon * 4;

    x_lo = lx_center - shell_extent_qr_wedge_mm / 2 - pocket_w / 2;
    x_hi = x_lo + pocket_w;

    // tread_slot_face_offset_mm pushes every tread pocket −Y off the +Y base face.
    y_top_lo = y_on_e_bevel_plane(z_lo) - ceiling_drop_mm - tread_slot_face_offset_mm - epsilon;
    y_top_hi = y_on_e_bevel_plane(z_hi) - ceiling_drop_mm - tread_slot_face_offset_mm - epsilon;
    y_bot_lo = y_top_lo - depth_y - z_pad;
    y_bot_hi = y_top_hi - depth_y - z_pad;

    if (z_lo + 0.2 < z_hi && y_top_lo > y_bot_lo + 0.2 && y_top_hi > y_bot_hi + 0.2)
        hull_rect_on_e_slope(
            x_lo,
            x_hi,
            z_lo - z_pad,
            z_hi + z_pad,
            y_top_lo,
            y_top_hi,
            y_bot_lo,
            y_bot_hi
        );
}

module shell_tread_groove_pocket_cube() {
    margin_x = (shell_extent_qr_wedge_mm - groove_w) / 2;
    x_hi = shell_extent_qr_wedge_mm - margin_x;
    x_lo = x_hi - groove_w;
    y_br = tread_groove_pocket_break_tread_face_mm;
    y_len = tread_groove_pocket_inward_y_mm + y_br;
    zh = tread_groove_pocket_height_mm + epsilon * 4;
    core_zh = tread_core_pocket_depth_z_mm + epsilon * 4;
    // Cutter 2: flange groove (wider), behind tread core toward F.
    shell_tread_pocket_sloped_hull(
        tread_pocket_lx_center_mm(),
        -y_br + y_len / 2 + tread_pocket_z_nudge_mm,
        groove_w,
        y_len,
        zh,
        core_zh
    );
}

// ceiling_drop_mm = 0 → ceiling flush on E bevel (tread 1, near side). A positive
// drop sinks the pocket past the flange groove for the back-to-back tread (tread 2).
// depth_z_mm sets how far the pocket runs along the bevel normal (the tread height
// proud of the flange); the buried inner tread needs more than the outer one.
module shell_tread_core_pocket_cube(ceiling_drop_mm = 0, depth_z_mm = tread_core_pocket_depth_z_mm) {
    margin_x = (shell_extent_qr_wedge_mm - tread_w) / 2;
    x_hi = shell_extent_qr_wedge_mm - margin_x;
    x_lo = x_hi - tread_w;
    y_br = tread_groove_pocket_break_tread_face_mm;
    y_len = tread_core_pocket_inward_y_mm + y_br;
    zh = depth_z_mm + epsilon * 4;
    // Cutter 3: tread core (narrower), ceiling flush on E bevel (or dropped for tread 2).
    shell_tread_pocket_sloped_hull(
        tread_pocket_lx_center_mm(),
        -y_br + y_len / 2 + tread_pocket_z_nudge_mm,
        tread_w,
        y_len,
        zh,
        ceiling_drop_mm
    );
}

// ── Tread retention cap fastener (body side) ────────────────────────────────
// Bolt channel: shaft bore running +Z from the mouth past the nut, on the
// central axis just behind the inner tread.
module tread_cap_bolt_channel() {
    d = cap_bolt_dia + cap_bolt_clearance;
    z0 = tread_cap_mouth_z_mm() - epsilon * 4;
    z1 = cap_bolt_tip_z_mm() + 0.5;
    translate([cap_bolt_x_bracket_mm(), cap_bolt_y_mm(), z0])
        cylinder(h = z1 - z0, d = d, $fn = preview ? 24 : 48);
}

// Hex nut seat — axis along Z (coaxial with the bolt); flats face ±X so the nut
// slides in along +Y (from the tread cavity) and keys against rotation. The seat
// is cap_nut_pocket_z_extra taller than the slide-in slot on each Z face, so its
// top/bottom shoulders trap the nut once seated (prayer-sole collar pattern).
module tread_cap_nut_pocket() {
    nut_r = (cap_nut_af + cap_nut_clearance) / 2 / cos(30);
    h = cap_nut_pocket_z_height_mm();
    translate([cap_bolt_x_bracket_mm(), cap_bolt_y_mm(), cap_nut_center_z_mm() - h / 2])
        rotate([0, 0, 30])
            cylinder(h = h, r = nut_r, $fn = 6);
}

// Nut slide-in slot — channel running +Y from the hex seat up into the tread-slot
// cavity (behind the inner tread). The nut drops in through the slot and slides −Y
// to seat; no exterior bracket face is broken. Its Z height is just the nut
// thickness + clearance (shorter than the seat), so the nut can't flop in the
// channel and the taller seat's shoulders retain it at the end.
module tread_cap_nut_slot() {
    w = cap_nut_af + cap_nut_clearance;   // X width (across flats; keys rotation)
    h = cap_nut_slot_z_height_mm();       // Z height (nut thickness + clearance, no seat extra)
    y_start = cap_bolt_y_mm();
    y_end = cap_nut_slot_exit_y_mm();
    len = abs(y_end - y_start);
    translate([cap_bolt_x_bracket_mm() - w / 2, min(y_start, y_end), cap_nut_center_z_mm() - h / 2])
        cube([w, len, h]);
}

// Cap recess ("cube hull"): a rectangular pocket in the −Z mouth, below the
// seated treads, that the flush cap plugs into. Cut from the body at inset = 0;
// the cap is built from the same volume shrunk by the fit clearance. The −Z face
// runs proud of the mouth and the top runs above E (the bevel/envelope clip the
// real faces), so only the −Y floor (wedge start), ±X sides, and +Z face matter.
module tread_cap_recess_volume(inset = 0) {
    x_lo = tread_cap_recess_x_lo_bracket_mm(inset);
    x_hi = tread_cap_recess_x_hi_bracket_mm(inset);
    y_lo = tread_cap_recess_y_lo_mm() + inset;
    y_hi = tread_cap_recess_y_hi_mm();
    z_lo = tread_cap_recess_z_lo_mm() - epsilon * 4;
    z_hi = tread_cap_recess_z_hi_mm() - inset;
    translate([x_lo, y_lo, z_lo])
        cube([x_hi - x_lo, y_hi - y_lo, z_hi - z_lo]);
}

// Body envelope with the E-bevel only (no tread pockets) — used to carve the cap
// so the plug is solid across the slot opening (stops the treads) yet still
// follows the bracket's beveled top and rounded mouth faces. The cap's +X extent
// is pulled flush with the mount-block −X face by tread_cap_recess_x_hi_mm (not
// carved by the angled undercut), so its pew-side edge stays flush full-length.
module shell_solid_no_tread_pockets() {
    difference() {
        shell_envelope_minkowski_union();
        shell_tread_face_de_bevel_cut();
    }
}

// Through-shaft + socket-head recess, cut from the cap's outer (−Z / mouth) face.
module tread_cap_bolt_hole() {
    shaft_d = cap_bolt_dia + cap_bolt_clearance;
    head_d  = cap_head_dia + cap_head_clearance + 0.1;
    z_outer = tread_cap_outer_z_mm();
    shaft_h = (tread_cap_recess_z_hi_mm() - z_outer) + epsilon * 8;
    translate([cap_bolt_x_bracket_mm(), cap_bolt_y_mm(), z_outer - epsilon * 4]) {
        cylinder(h = shaft_h, d = shaft_d);
        cylinder(h = cap_head_height + epsilon * 4, d = head_d);
    }
}

// Flush plug: recess volume (optionally shrunk for slip fit) ∩ beveled body solid.
// cut_bolt_hole=false for fused bracket export — shell_body_with_integrated_cap()
// subtracts tread_cap_bolt_hole() after the cap is unioned into the body.
module tread_cap_solid(inset = cap_fit_clearance_mm, cut_bolt_hole = true) {
    union() {
        difference() {
            intersection() {
                shell_solid_no_tread_pockets();
                tread_cap_recess_volume(inset);
            }
            if (cut_bolt_hole)
                tread_cap_bolt_hole();
        }
        cap_guide_pins();
    }
}

module tread_cap() {
    tread_cap_solid();
}

// Guide pins protruding +X from the cap's pew-side face: a cylinder (root buried
// in the cap for fusion) capped by a domed tip for lead-in. Added to the cap.
module cap_guide_pins() {
    if (cap_guide_pin_enable) {
        x_face = tread_cap_face_x_bracket_mm();
        for (y = cap_guide_pin_y_positions) {
            translate([x_face - cap_guide_pin_cap_overlap_mm, y, cap_guide_pin_z_mm])
                rotate([0, 90, 0])   // local +Z → +X
                    cylinder(
                        h = cap_guide_pin_cap_overlap_mm + cap_guide_pin_len_mm,
                        r = cap_guide_pin_radius_mm,
                        $fn = preview ? 16 : 32
                    );
            translate([x_face + cap_guide_pin_len_mm, y, cap_guide_pin_z_mm])
                sphere(r = cap_guide_pin_dome_r_mm, $fn = preview ? 16 : 32);
        }
    }
}

// Matching clearance bores in the bracket's pew-side wall, with a conical mouth
// lead-in so the pin can cock as the cap pivots into the mouth. Subtracted from
// the body.
module cap_guide_pin_holes() {
    if (cap_guide_pin_enable) {
        x_face = tread_cap_face_x_bracket_mm();
        x0 = x_face - cap_guide_pin_cap_overlap_mm - epsilon;        // start in the gap, ahead of the pin root
        x1 = x_face + cap_guide_pin_len_mm + cap_guide_pin_hole_extra_mm;  // past the domed tip
        r_bore = cap_guide_pin_radius_mm + cap_guide_pin_hole_clear_mm;
        for (y = cap_guide_pin_y_positions) {
            translate([x0, y, cap_guide_pin_z_mm])
                rotate([0, 90, 0])
                    cylinder(h = x1 - x0, r = r_bore, $fn = preview ? 16 : 32);
            // Conical lead-in at the recess-wall mouth (wide at the wall, tapering in).
            if (cap_guide_pin_mouth_chamfer_mm > 0)
                translate([tread_cap_recess_x_hi_bracket_mm() - epsilon, y, cap_guide_pin_z_mm])
                    rotate([0, 90, 0])
                        cylinder(
                            h = cap_guide_pin_mouth_chamfer_mm + epsilon,
                            r1 = r_bore + cap_guide_pin_mouth_chamfer_mm,
                            r2 = r_bore,
                            $fn = preview ? 16 : 32
                        );
        }
    }
}

module tread_cap_fastener_cuts() {
    if (tread_cap_enabled) {
        tread_cap_bolt_channel();
        tread_cap_nut_pocket();
        tread_cap_nut_slot();
    }
}

// Preview hardware (assembly only): silver bolt seated in the cap + green nut.
module tread_cap_hardware_debug() {
    head_top_z = tread_cap_outer_z_mm();
    color("silver", 0.85) {
        translate([cap_bolt_x_bracket_mm(), cap_bolt_y_mm(), head_top_z])
            cylinder(h = cap_head_height, d = cap_head_dia, $fn = 40);
        translate([cap_bolt_x_bracket_mm(), cap_bolt_y_mm(), cap_bolt_head_end_z_mm()])
            cylinder(h = cap_bolt_length, d = cap_bolt_dia, $fn = 28);
    }
    nut_r = cap_nut_af / 2 / cos(30);
    color("green", 0.7)
        translate([cap_bolt_x_bracket_mm(), cap_bolt_y_mm(), cap_nut_center_z_mm() - cap_nut_thickness / 2])
            rotate([0, 0, 30])
                cylinder(h = cap_nut_thickness, r = nut_r, $fn = 6);
}

// Place a 2D profile (children) onto the mount block's tilted +Y front face and
// engrave it depth mm inward (−Y along the face normal), centered on the QR tile
// position. Lie the profile on the tilted front face: pivot at the +X (pew-flush)
// edge of the pre-mink front line, rotate the frame by the face angle about Z,
// then sit it on the plane. The actual face sits corner_r out along the tilted
// normal (minkowski skin), so push out by corner_r and add a corner_r*sin term to
// `along` so the normal offset's X-component doesn't shift the profile off-center.
// (Both side edges of the visible face are planar trims at exactly x_lo / x_hi —
// see pew_mount_block_face_angle_deg in config.scad — so centering on the nominal
// (x_lo + x_hi)/2 centers on the visible face too.)
module qr_face_engrave(depth) {
    x_piv = pew_mount_block_face_x_hi_mm();
    xc = pew_mount_block_face_center_x_mm() + qr_pocket_x_offset_mm;
    zc = pew_mount_block_z_center_mm() + qr_pocket_z_offset_mm;
    along = (xc - x_piv + corner_r * sin(pew_mount_block_face_angle_deg))
        / cos(pew_mount_block_face_angle_deg);
    translate([x_piv, pew_mount_block_face_flat_y_mm(), pew_mount_block_z_center_mm()])
        rotate([0, 0, pew_mount_block_face_angle_deg])
            translate([along, corner_r + epsilon, zc - pew_mount_block_z_center_mm()])
                rotate([90, 0, 0])   // extrude axis (+Z local) → face inward normal
                    linear_extrude(depth + epsilon)
                        children();
}

// Rounded square, corner radius r, centered on the origin.
module qr_rounded_square_2d(size, r_in) {
    r = min(r_in, size / 2 - 0.01);
    half = size / 2 - r;
    hull()
        for (a = [-1, 1], b = [-1, 1])
            translate([a * half, b * half])
                circle(r = r, $fn = preview ? 16 : 32);
}

// Rounded-square recess on the mount block's +Y front face: a self-aligning
// fence for the 1" QR-code sticker. Cuts qr_pocket_depth_mm inward (−Y) with
// qr_pocket_clearance_mm of gap per side so the tile drops in and the pocket
// walls register it. Centered on that face (offsets nudge it along bracket X/Z).
module qr_sticker_pocket() {
    qr_face_engrave(qr_pocket_depth_mm)
        qr_rounded_square_2d(
            qr_pocket_size_mm + 2 * qr_pocket_clearance_mm,
            qr_pocket_corner_r_mm);
}

// Engraved alignment frame around the sticker recess (bait-station style): a
// thin square groove qr_frame_gap_mm outside the tile edge so the sticker can
// be sighted into place. Corner radii grow with the offset so the groove width
// stays constant around the corners.
module qr_frame_groove() {
    inner = qr_pocket_size_mm + 2 * qr_frame_gap_mm;
    outer = inner + 2 * qr_frame_line_w_mm;
    qr_face_engrave(qr_frame_depth_mm)
        difference() {
            qr_rounded_square_2d(outer, qr_pocket_corner_r_mm + qr_frame_gap_mm + qr_frame_line_w_mm);
            qr_rounded_square_2d(inner, qr_pocket_corner_r_mm + qr_frame_gap_mm);
        }
}

// Vertical pocket ("cube hull") in the +X (pew-leg) face of the mount block.
// Opens on +X (overshoots the minkowski skin), runs depth_x in −X, and spans
// the block's full Z length (overshoots both Z ends). The +Y window is taken
// from the block's roof-side (−Y) end.
module pew_mount_block_pocket_cut() {
    x_face = pew_mount_block_face_x_mm();
    x_hi = x_face + corner_r + epsilon * 4;            // clear the rounded exterior
    x_lo = x_face - pew_mount_block_pocket_depth_x_mm;
    y_lo = pew_mount_block_pocket_y_lo_mm();
    y_hi = pew_mount_block_pocket_y_hi_mm();
    z_half = pew_mount_block_z_len_mm() / 2 + corner_r + epsilon * 4;
    z_lo = pew_mount_block_z_center_mm() - z_half;
    z_hi = pew_mount_block_z_center_mm() + z_half;
    translate([x_lo, y_lo, z_lo])
        cube([x_hi - x_lo, y_hi - y_lo, z_hi - z_lo]);
}

// Plane off everything +X of the pew leg inner face, flattening the mount
// block's rounded pew-facing skin so it beds flush against the pew (no overshoot,
// no rounding). Only the mount block reaches this far in +X.
module pew_mount_block_pew_face_trim() {
    flush_x = assembly_pew_leg_inner_face_x_mm();
    big = _bracket_cross_half_extent();
    translate([flush_x, -big, -big])
        cube([2 * big, 2 * big, 2 * big]);
}

// "Hull off" the lower portion of the block + angled plate: a flat ceiling at
// undercut_top_z runs from the +Y front face back to a ramp that closes down to
// the block bottom flush with the pew-side pocket's −Y edge ("the bridge"). Built
// as the hull of a flat-ceiling slab (front) and a thin bottom edge (at the
// bridge). Full combined width, overshooting the minkowski skin on the open
// sides (−X reinforcement, +X pew face, +Y front, −Z bottom).
module pew_mount_block_bottom_undercut_cut() {
    over = corner_r + epsilon * 4;
    x_lo = pew_mount_block_undercut_x_lo_mm();           // through the −X reinforcement skin
    x_hi = pew_mount_block_face_x_hi_mm() + over;        // out past the +X pew-flush face
    z_top = pew_mount_block_undercut_top_z_mm;           // flat ceiling (halfway up)
    z_bot = pew_mount_block_z_lo_mm() - over;            // below the block bottom
    y_front = pew_mount_block_face_flat_y_mm() + over;   // past the +Y front
    y_ramp = pew_mount_block_undercut_ramp_start_y_mm(); // flat ends / ramp begins
    y_bridge = pew_mount_block_undercut_y_lo_mm();       // ramp lands at the pocket −Y edge

    hull() {
        // Flat-ceiling slab over the front portion.
        translate([x_lo, y_ramp, z_bot])
            cube([x_hi - x_lo, y_front - y_ramp, z_top - z_bot]);
        // Thin bottom edge at the bridge: the ramp tapers the ceiling to here.
        translate([x_lo, y_bridge, z_bot])
            cube([x_hi - x_lo, epsilon, epsilon]);
    }
}

// Angled bore + flat-head countersink for a #8 wood screw that mounts the bracket
// to the pew leg. The screw enters the angled +Y front face at its geometric
// centre (behind the QR sticker) and exits the +X pew-flush face. Half the face
// angle keeps the axis on the face bisector: it passes through the face centre
// regardless of the angle magnitude.
//
// Coordinate note (in the rotated local frame established below):
//   local +Z  →  [cos(ang), -sin(ang), 0] in bracket frame  (toward +X pew face)
//   local -Z  →  outside the angled face  (countersink/head side)
// Bore + perpendicular flat-head chamfer for a #8 wood screw that mounts the
// bracket to the pew. The bore runs primarily along +Y (from the −X reinforcement
// face toward the angled +Y front face), tilted 10° toward +X in the XY plane so
// it exits at the geometric centre of the angled face. The screw head sits in a
// circular countersink on the −X reinforcement face (axis perpendicular to that
// face = along +X), which is the accessible inner face of the mount block.
//
// Local bore frame (set up by the two rotations below):
//   local +Z  →  [sin(ang), cos(ang), 0]  (bore direction; toward angled face)
//   z = 0       = entry on −X reinforcement face
//   z = t_exit  = exit at angled face centre
module side_screw_shaft() {
    if (side_screw_enabled && pew_mount_block_enabled && pew_mount_block_y_len_mm > 0.2) {
        ang   = side_screw_angle_deg;
        r_sh  = side_screw_dia_mm / 2;
        fn    = preview ? 16 : 32;
        over  = corner_r + epsilon * 4;

        x_c  = side_screw_bore_x_mm;
        y_c  = side_screw_bore_y_mm;
        z_c  = side_screw_bore_z_mm;
        x_hi = side_screw_bore_x_hi_mm;

        // Bore direction: [cos(ang), −sin(ang), 0] — mostly +X, slight −Y.
        dist_to_pew = (x_hi - x_c) / cos(ang);

        translate([x_c, y_c, z_c])
            rotate([0, 0, -ang])
                rotate([0, 90, 0])
                    translate([0, 0, -over])
                        cylinder(h = dist_to_pew + 2 * over, r = r_sh, $fn = fn);
    }
}

module side_screw_chamfer() {
    if (side_screw_enabled && pew_mount_block_enabled && pew_mount_block_y_len_mm > 0.2) {
        ang      = side_screw_angle_deg;
        r_sh     = side_screw_dia_mm / 2;
        r_hd     = side_screw_head_dia_mm / 2 + side_screw_chamfer_lip_mm;
        half_ang = (180 - side_screw_chamfer_deg) / 2;
        ch_d     = (r_hd - r_sh) / tan(half_ang);
        fn       = preview ? 16 : 32;
        over     = corner_r + epsilon * 4;

        x_c = side_screw_bore_x_mm;
        y_c = side_screw_bore_y_mm;
        z_c = side_screw_bore_z_mm;
        recess = side_screw_chamfer_recess_mm;
        bridge_face = side_screw_chamfer_bridge_face_mm;
        inward  = [ cos(ang), -sin(ang), 0];
        outward = [-cos(ang),  sin(ang), 0];

        // Chamfer on the angled +Y entry face (accessible from the QR-code / front side).
        // Recess along the bore axis so the flat-head lip clears the tilted face skin; a
        // cylindrical hull bridges outward to the skin and inward to the countersink mouth.
        translate([x_c, y_c, z_c]) {
            if (recess > epsilon || bridge_face > epsilon)
                hull() {
                    translate(outward * bridge_face)
                        rotate([0, 0, 180 - ang])
                            rotate([0, 90, 0])
                                cylinder(h = over, r = r_hd, $fn = fn);
                    translate(inward * recess)
                        rotate([0, 0, -ang])
                            rotate([0, 90, 0])
                                translate([0, 0, -epsilon * 4])
                                    cylinder(h = epsilon * 4, r = r_hd, $fn = fn);
                }
            translate(inward * recess)
                rotate([0, 0, -ang])
                    rotate([0, 90, 0])
                        cylinder(h = ch_d + over, r1 = r_hd, r2 = r_sh, $fn = fn);
        }
    }
}

module shell_body_main_difference() {
    // Filleted core+prism+mount pad minus three sloped hull cutters (bevel + flange + tread).
    // The bottom undercut is applied pre-minkowski (undercut = true) so its edges fillet.
    difference() {
        shell_envelope_minkowski_union(undercut = true);
        shell_tread_face_de_bevel_cut();
        if (tread_groove_shell_pocket_enabled)
            shell_tread_groove_pocket_cube();
        if (tread_core_shell_pocket_enabled)
            shell_tread_core_pocket_cube();
        if (tread_core_shell_pocket_2_enabled)
            shell_tread_core_pocket_cube(
                tread_core_pocket_2_ceiling_drop_mm,
                tread_core_pocket_2_depth_z_mm
            );
        if (wood_screw_holes_enabled)
            wood_screw_shank_pattern();
        if (tread_cap_enabled && tread_cap_separate_print)
            tread_cap_recess_volume();
        tread_cap_fastener_cuts();
        if (qr_pocket_enabled)
            qr_sticker_pocket();
        if (qr_frame_enabled)
            qr_frame_groove();
        if (pew_mount_block_pocket_enabled && pew_mount_block_enabled && pew_mount_block_y_len_mm > 0.2)
            pew_mount_block_pocket_cut();
        if (pew_mount_block_pew_face_flush_enabled && pew_mount_block_enabled)
            pew_mount_block_pew_face_trim();
        if (tread_cap_enabled && tread_cap_separate_print)
            cap_guide_pin_holes();
        if (side_screw_enabled && pew_mount_block_enabled && pew_mount_block_y_len_mm > 0.2)
            side_screw_shaft();
    }
}

module shell_body_difference_wedge_bores() {
    if (tread_cap_enabled && !tread_cap_separate_print)
        shell_body_with_integrated_cap()
            shell_body_main_difference();
    else
        difference() {
            shell_body_main_difference();
            shell_body_late_screw_cuts();
        }
}

module bumper_bracket() {
    bracket_export_bed_lift()
        bracket_cross_trim() {
            bumper_bracket_shell_body();
            bumper_bracket_debug_face_labels();
        }
}

module _bumper_debug_label_plate() {
    cube([bumper_bracket_debug_label_plate_mm, bumper_bracket_debug_label_plate_mm, 0.6], center = true);
}

module _bumper_debug_label_glyph(letter, plate_color, text_color) {
    color(plate_color)
        _bumper_debug_label_plate();
    color(text_color)
        linear_extrude(bumper_bracket_debug_label_thickness_mm)
            offset(delta = 0.6, chamfer = 0.3)
                text(
                    letter,
                    size = bumper_bracket_debug_label_size_mm,
                    font = bumper_bracket_debug_label_font,
                    halign = "center",
                    valign = "center"
                );
}

// Bracket-frame labels (assembly preview only; not in STL export root).
module bumper_bracket_debug_face_labels() {
    if (bumper_bracket_debug_face_labels_enabled) {
        off = bumper_bracket_debug_label_offset_mm;
        y_mid = shell_midplane_y_mm;
        x_out = bracket_face_wedge_x_mm + off;
        x_in = -bracket_face_wedge_x_mm - off;
        z_pew = bracket_face_pew_z_mm + off;
        z_tread = bracket_face_tread_slot_z_mm - off;
        y_base = bracket_nat_y_mid_mm - corner_r + off;
        y_roof_out = bracket_nat_y_mid_mm - shell_height_mm - shell_wedge_leg_mm - off
            - bumper_bracket_debug_label_thickness_mm;
        translate([x_out, y_mid, 0])
            rotate([0, 90, 0])
                _bumper_debug_label_glyph("A", [1, 0.2, 0.2], [1, 1, 1]);
        translate([x_in, y_mid, 0])
            rotate([0, -90, 0])
                _bumper_debug_label_glyph("B", [0.2, 1, 0.2], [0, 0, 0]);
        translate([0, y_mid, z_pew])
            rotate([-90, 0, 0])
                _bumper_debug_label_glyph("C", [0.2, 0.4, 1], [1, 1, 1]);
        translate([0, y_mid, z_tread])
            rotate([90, 0, 0])
                _bumper_debug_label_glyph("D", [0.9, 0.85, 0.1], [0, 0, 0]);
        translate([0, y_base, 0])
            rotate([-90, 0, 0])
                _bumper_debug_label_glyph("E", [0.2, 0.85, 0.4], [1, 1, 1]);
        translate([0, y_roof_out, 0])
            rotate([90, 0, 0])
                _bumper_debug_label_glyph("F", [0.6, 0.2, 0.8], [1, 1, 1]);
    }
}

if (is_undef(BUMPER_BRACKET_INCLUDED_BY))
    bumper_bracket();
