cesau78/tektonology/3d-models/bumper-bracket/kneeler-bumper-visual.scad

// Assembly ghost — kneeler-bumper.scad. Base at z = 0 mates peg support boss top.

module kneeler_bumper_visual_for_exploded_view() {
    difference() {
        cylinder(h = kneeler_bumper_height_mm, d = kneeler_bumper_od_mm);
        translate([0, 0, -epsilon])
            cylinder(h = kneeler_bumper_height_mm + 2 * epsilon, d = kneeler_bumper_id_mm);
    }
}
