cesau78/tektonology/3d-models/prayer-sole/v3-compound-fastened/stamp-common.scad

// Product info deboss (lines from stamp-generated.scad; export script writes it).
// Top face: mates against coupler — hidden when assembled.

include <stamp-generated.scad>

kbc_info_stamp_depth = 1.2;

kbc_mark_size = 5;
kbc_mark_size_secondary = 3.5;
kbc_mark_size_tertiary = 3.5;
kbc_mark_gap_2_3 = kbc_mark_size_secondary * 1.25;
// Vertical gap between stamp lines 3 and 4 (line 2–3 spacing uses kbc_mark_gap_2_3).
kbc_mark_gap_3_4 = kbc_mark_gap_2_3;
kbc_mark_gap_extra_brand_to_product = 2.5;
kbc_mark_gap_1_2 = kbc_mark_gap_2_3 + kbc_mark_gap_extra_brand_to_product;
kbc_mark_rule_adv_per_char = 0.78;
kbc_mark_rule_stroke_scale = 0.132;
kbc_mark_rule_right_inset = 0.40;
// Line 1 uses valign=center; this estimates how far below that center the lowest descender (e.g. “y”) ends, in × line1 size. Rule top is placed flush with that Y.
kbc_mark_rule_line1_descender_factor = 0.50;
// Rectangular tread: keep 0 so the stack stays centered on the top face (+Y rim shift is for round parts).
kbc_mark_radial_shift_fraction = 0;
kbc_mark_font = "Consolas:style=Bold";
// Per-line overrides (custom tread .scad files can set these after include <tread.scad>).
info_stamp_line1_size = kbc_mark_size;
info_stamp_line2_size = kbc_mark_size_secondary;
info_stamp_line3_size = kbc_mark_size_secondary;
info_stamp_line4_size = kbc_mark_size_tertiary;
info_stamp_line1_font = kbc_mark_font;
info_stamp_line2_font = kbc_mark_font;
info_stamp_line3_font = kbc_mark_font;
info_stamp_line4_font = kbc_mark_font;
info_stamp_line1_halign = "center";
info_stamp_line1_valign = "center";
info_stamp_line2_halign = "center";
info_stamp_line2_valign = "center";
info_stamp_line3_halign = "center";
info_stamp_line3_valign = "center";
info_stamp_line4_halign = "center";
info_stamp_line4_valign = "center";
info_stamp_line1_smallcaps = 4;
info_stamp_line2_smallcaps = 3;
info_stamp_line3_smallcaps = 3;
info_stamp_line4_smallcaps = 3;
info_stamp_line1_spacing = 1.2;
info_stamp_line2_spacing = 1.1;
info_stamp_line3_spacing = 1.1;
info_stamp_line4_spacing = 1.1;
info_stamp_line1_rule = true;
info_stamp_gap_1_2 = kbc_mark_gap_1_2;

// Custom stamp layouts: non-empty list switches line source to profile rows (legacy line1..4 ignored for text).
// Segmented format (recommended): each row is [halign, valign, [segment, ...]]
//   Segment: [text, size] or [text, size, font] or [text, size, font, smallcaps_size, spacing]
// Legacy flat format (auto-detected when row[2] is not a list): ["text", size, "font", "halign", sc, spacing]
info_stamp_profile = [];
// Optional [ gap row0–1, row1–2, ... ]; empty [] uses kbc_mark_gap_2_3 (segmented) or per-line defaults (legacy).
info_stamp_gaps = [];

function stamp_default_size_for_line(i) =
    i == 0 ? kbc_mark_size
    : i == 3 ? kbc_mark_size_tertiary
    : kbc_mark_size_secondary;

function stamp_prof_text(row) = row[0];
function stamp_prof_size(row, i) =
    len(row) >= 2 ? row[1] : stamp_default_size_for_line(i);
function _stamp_row_sc_shorthand(row) = len(row) >= 3 && is_num(row[2]);
function stamp_prof_font(row, def) =
    len(row) >= 3 && is_string(row[2]) ? row[2] : def;
function stamp_prof_h(row, def) =
    _stamp_row_sc_shorthand(row) ? def :
    len(row) >= 4 && is_string(row[3]) ? row[3] : def;
function stamp_prof_sc(row) =
    _stamp_row_sc_shorthand(row) ? row[2] :
    len(row) >= 4 && is_num(row[3]) ? row[3] :
    len(row) >= 5 && is_num(row[4]) ? row[4] : 0;
function stamp_prof_spacing(row) =
    _stamp_row_sc_shorthand(row)
        ? (len(row) >= 4 && is_num(row[3]) ? row[3] : 1)
        : (len(row) >= 6 && is_num(row[5]) ? row[5] : 1);

function stamp_use_profile() = len(info_stamp_profile) > 0;

function stamp_legacy_text(i) =
    i == 0 ? info_stamp_line1
    : i == 1 ? info_stamp_line2
    : i == 2 ? info_stamp_line3
    : info_stamp_line4;

function stamp_eff_text(i) =
    stamp_use_profile()
        ? (i < len(info_stamp_profile) ? stamp_prof_text(info_stamp_profile[i]) : "")
        : stamp_legacy_text(i);

function stamp_legacy_size(i) =
    i == 0 ? info_stamp_line1_size
    : i == 1 ? info_stamp_line2_size
    : i == 2 ? info_stamp_line3_size
    : info_stamp_line4_size;

function stamp_eff_size(i) =
    stamp_use_profile() && i < len(info_stamp_profile)
        ? stamp_prof_size(info_stamp_profile[i], i)
        : stamp_legacy_size(i);

function stamp_legacy_font(i) =
    i == 0 ? info_stamp_line1_font
    : i == 1 ? info_stamp_line2_font
    : i == 2 ? info_stamp_line3_font
    : info_stamp_line4_font;

function stamp_eff_font(i) =
    stamp_use_profile() && i < len(info_stamp_profile)
        ? stamp_prof_font(info_stamp_profile[i], kbc_mark_font)
        : stamp_legacy_font(i);

function stamp_legacy_h(i) =
    i == 0 ? info_stamp_line1_halign
    : i == 1 ? info_stamp_line2_halign
    : i == 2 ? info_stamp_line3_halign
    : info_stamp_line4_halign;

function stamp_eff_h(i) =
    stamp_use_profile() && i < len(info_stamp_profile)
        ? stamp_prof_h(info_stamp_profile[i], "center")
        : stamp_legacy_h(i);

function stamp_legacy_sc(i) =
    i == 0 ? info_stamp_line1_smallcaps
    : i == 1 ? info_stamp_line2_smallcaps
    : i == 2 ? info_stamp_line3_smallcaps
    : info_stamp_line4_smallcaps;

function stamp_eff_sc(i) =
    stamp_use_profile() && i < len(info_stamp_profile)
        ? stamp_prof_sc(info_stamp_profile[i])
        : stamp_legacy_sc(i);

function stamp_legacy_spacing(i) =
    i == 0 ? info_stamp_line1_spacing
    : i == 1 ? info_stamp_line2_spacing
    : i == 2 ? info_stamp_line3_spacing
    : info_stamp_line4_spacing;

function stamp_eff_spacing(i) =
    stamp_use_profile() && i < len(info_stamp_profile)
        ? stamp_prof_spacing(info_stamp_profile[i])
        : stamp_legacy_spacing(i);

// --- Small Caps ---
// Renders lowercase letters as uppercase at a reduced size, baseline-aligned.
// sc_advance_factor: average character advance as fraction of font size.
// Default matches kbc_mark_rule_adv_per_char; override per-tread to tune spacing.
sc_advance_factor = 0.64;

function _sc_is_lower(ch) = let(c = ord(ch)) (c != undef && c >= 97 && c <= 122);
function _sc_upper(ch) = _sc_is_lower(ch) ? chr(ord(ch) - 32) : ch;

function _sc_ch_advance(ch, full_sz, sc_sz, sp=1) =
    let(rsz = _sc_is_lower(ch) ? sc_sz : full_sz)
    sc_advance_factor * rsz * sp;

function _sc_total_w(s, fsz, ssz, sp=1, i=0) =
    i >= len(s) ? 0 :
    _sc_ch_advance(s[i], fsz, ssz, sp) + _sc_total_w(s, fsz, ssz, sp, i+1);

function _sc_x_at(s, fsz, ssz, idx, sp=1, i=0) =
    i >= idx ? 0 :
    _sc_ch_advance(s[i], fsz, ssz, sp) + _sc_x_at(s, fsz, ssz, idx, sp, i+1);

module _smallcaps_line(s, size, sc_size, font, halign="center", spacing=1) {
    tw = _sc_total_w(s, size, sc_size, spacing);
    x0 = (halign == "center") ? -tw/2 :
         (halign == "right")  ? -tw : 0;
    y0 = -size * 0.35;
    translate([x0, y0, 0])
        for (i = [0 : max(0, len(s)-1)]) {
            ch = s[i];
            rch = _sc_upper(ch);
            rsz = _sc_is_lower(ch) ? sc_size : size;
            translate([_sc_x_at(s, size, sc_size, i, spacing), 0, 0])
                text(rch, size=rsz, font=font, halign="left", valign="baseline");
        }
}

function _map_valign(v) = v == "top" ? "top" : v == "bottom" ? "bottom" : "center";

module _stamp_text(s, size, sc_size, font, halign, spacing=1, valign="center") {
    if (sc_size > 0)
        _smallcaps_line(s, size, sc_size, font, halign, spacing);
    else
        text(s, size=size, font=font, halign=halign, valign=valign, spacing=spacing);
}

// --- Segmented profile format ---
// Row: [halign, valign, [segment, ...]]
// Segment: [text, size] or [text, size, font] or [text, size, font, smallcaps_size, spacing]

function _is_segmented_profile() =
    len(info_stamp_profile) > 0 && is_list(info_stamp_profile[0][2]);

function _seg_text(seg) = seg[0];
function _seg_size(seg) = seg[1];
function _seg_font(seg, def) = len(seg) >= 3 && is_string(seg[2]) ? seg[2] : def;
function _seg_sc(seg) = len(seg) >= 4 && is_num(seg[3]) ? seg[3] : 0;
function _seg_spacing(seg) = len(seg) >= 5 && is_num(seg[4]) ? seg[4] : 1;
function _seg_underline(seg) = len(seg) >= 6 && seg[5] == true;
function _seg_underline_scale(seg) = len(seg) >= 7 && is_num(seg[6]) ? seg[6] : 1;
function _seg_underline_x_offset(seg) = len(seg) >= 8 && is_num(seg[7]) ? seg[7] : 0;
function _seg_underline_y_offset(seg) = len(seg) >= 9 && is_num(seg[8]) ? seg[8] : 0;

function _row_halign(row) = row[0];
function _row_valign(row) = row[1];
function _row_segments(row) = row[2];
function _row_x_offset(row) = len(row) >= 4 && is_num(row[3]) ? row[3] : 0;
function _row_y_offset(row) = len(row) >= 5 && is_num(row[4]) ? row[4] : 0;
function _row_max_size(row) = max([for (s = _row_segments(row)) _seg_size(s)]);

function _seg_est_width(seg) =
    let(
        t = _seg_text(seg), sz = _seg_size(seg),
        sc = _seg_sc(seg), sp = _seg_spacing(seg)
    )
    sc > 0 ? _sc_total_w(t, sz, sc, sp) : len(t) * sz * sc_advance_factor * sp;

function _row_total_width(segs, i=0) =
    i >= len(segs) ? 0 : _seg_est_width(segs[i]) + _row_total_width(segs, i+1);

function _seg_x_at(segs, idx, i=0) =
    i >= idx ? 0 : _seg_est_width(segs[i]) + _seg_x_at(segs, idx, i+1);

function _row_char_count(segs, i=0) =
    i >= len(segs) ? 0 : len(_seg_text(segs[i])) + _row_char_count(segs, i+1);

// True when every character in s is a-z (used to decide whether the tallest
// glyph in a smallcaps segment is size or sc_size).
function _all_lower(s, i=0) =
    i >= len(s) ? true :
    (!_sc_is_lower(s[i]) ? false : _all_lower(s, i+1));

// Effective visual height: the size of the tallest rendered glyph.
function _seg_eff_height(seg) =
    let(sc = _seg_sc(seg), sz = _seg_size(seg))
    sc > 0 ? (_all_lower(_seg_text(seg)) ? sc : sz) : sz;

function _row_max_eff_height(segs, i=0) =
    i >= len(segs) ? 0 : max(_seg_eff_height(segs[i]), _row_max_eff_height(segs, i+1));

function _stamp_seg_y(i, gaps, default_gap) =
    i == 0 ? 0 : _stamp_seg_y(i-1, gaps, default_gap) -
    (i-1 < len(gaps) ? gaps[i-1] : default_gap);

// Y of the em-box center relative to the segment origin for each valign mode.
function _va_center_y(sz, va) =
    va == "top" ? -sz/2 : va == "bottom" ? sz/2 : 0;

module _stamp_segment_row(segs, halign, valign, default_font) {
    text_va = _map_valign(valign);

    // Single-segment rows: use the font engine's native halign for accurate
    // centering (important for proportional fonts). Multi-segment rows must
    // use estimated advances for relative layout.
    if (len(segs) == 1) {
        seg = segs[0];
        _stamp_text(_seg_text(seg), _seg_size(seg), _seg_sc(seg),
                    _seg_font(seg, default_font), halign, _seg_spacing(seg),
                    text_va);
        if (_seg_underline(seg)) {
            seg_w = _seg_est_width(seg);
            seg_sz = _seg_size(seg);
            ul_pad = seg_sz * sc_advance_factor * 0.5;
            ul_w = (seg_w + ul_pad) * _seg_underline_scale(seg);
            ul_dx = _seg_underline_x_offset(seg);
            ul_dy = _seg_underline_y_offset(seg);
            rule_t = max(0.28, seg_sz * kbc_mark_rule_stroke_scale);
            cy = _va_center_y(seg_sz, text_va);
            uy = cy - seg_sz * kbc_mark_rule_line1_descender_factor - rule_t / 2 - ul_dy;
            if (ul_w > 1)
                translate([ul_dx, uy, 0])
                    square([ul_w, rule_t], center = true);
        }
    } else {
        tw = _row_total_width(segs);
        x0 = (halign == "center") ? -tw/2 :
             (halign == "right") ? -tw : 0;
        for (i = [0 : max(0, len(segs)-1)]) {
            seg = segs[i];
            seg_x = x0 + _seg_x_at(segs, i);
            translate([seg_x, 0, 0])
                _stamp_text(_seg_text(seg), _seg_size(seg), _seg_sc(seg),
                            _seg_font(seg, default_font), "left", _seg_spacing(seg),
                            text_va);
            if (_seg_underline(seg)) {
                seg_w = _seg_est_width(seg);
                seg_sz = _seg_size(seg);
                ul_pad = seg_sz * sc_advance_factor * 0.5;
                ul_w = (seg_w + ul_pad) * _seg_underline_scale(seg);
                ul_dx = _seg_underline_x_offset(seg);
                ul_dy = _seg_underline_y_offset(seg);
                rule_t = max(0.28, seg_sz * kbc_mark_rule_stroke_scale);
                cy = _va_center_y(seg_sz, text_va);
                uy = cy - seg_sz * kbc_mark_rule_line1_descender_factor - rule_t / 2 - ul_dy;
                if (ul_w > 1)
                    translate([seg_x + ul_w / 2 + ul_dx, uy, 0])
                        square([ul_w, rule_t], center = true);
            }
        }
    }
}

module _stamp_deboss_segmented(z_top, radial_ref, text_x_half=0) {
    depth = kbc_info_stamp_depth + 0.02;
    _tx_inset = 1.5;
    _tx_edge = text_x_half > 0 ? text_x_half - _tx_inset : 0;
    n = len(info_stamp_profile);
    default_gap = kbc_mark_gap_2_3;
    stamp_shift_y = radial_ref * kbc_mark_radial_shift_fraction;

    ys = [for (i = [0:n-1]) _stamp_seg_y(i, info_stamp_gaps, default_gap)];
    sizes = [for (i = [0:n-1]) _row_max_size(info_stamp_profile[i])];
    bbox_top = ys[0] + sizes[0] / 2;
    bbox_bot = ys[n-1] - sizes[n-1] / 2;
    center_adj = -(bbox_top + bbox_bot) / 2;

    translate([0, stamp_shift_y, z_top + 0.01])
        rotate([180, 0, 0])
        mirror([1, 0, 0])
        translate([0, center_adj, 0]) {
            for (i = [0 : n-1]) {
                row = info_stamp_profile[i];
                halign = _row_halign(row);
                va = _row_valign(row);
                segs = _row_segments(row);
                hx = _tx_edge > 0 ? (halign == "left" ? -_tx_edge :
                     halign == "right" ? _tx_edge : 0) : 0;
                // Gap system assumes valign="center"; compensate for top/bottom
                // so the row occupies the same vertical space as a centered row.
                va_adj = _va_center_y(sizes[i], _map_valign(va));

                linear_extrude(depth)
                    translate([hx + _row_x_offset(row), ys[i] - va_adj - _row_y_offset(row), 0])
                        _stamp_segment_row(segs, halign, va, kbc_mark_font);
            }
        }
}

// Deboss on the top flat (z = z_top), read from above into the coupler socket.
module part_top_info_stamp_deboss(enable, z_top, radial_ref, text_x_half=0) {
    if (enable && _is_segmented_profile()) {
        _stamp_deboss_segmented(z_top, radial_ref, text_x_half);
    } else {
        _stamp_deboss_classic(enable, z_top, radial_ref, text_x_half);
    }
}
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
